davidsmakerworks/fencing-analyzer/FencingAnalyzer.X/configbits.c

/*
 * Fencing Action Analyzer
 * Copyright (c) 2020 David Rice
 * 
 * Configuration bit settings
 * 
 * SET/CLR/INV registers are used when appropriate to avoid
 * R-M-W hazards on MIPS architecture, but "bits" structures
 * are used for readability when no R-M-W hazard exists.
 *
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
 * THE SOFTWARE IS PROVIDED "AS IS", WITHOUT WARRANTY OF ANY KIND, EXPRESS OR
 * IMPLIED, INCLUDING BUT NOT LIMITED TO THE WARRANTIES OF MERCHANTABILITY,
 * FITNESS FOR A PARTICULAR PURPOSE AND NONINFRINGEMENT. IN NO EVENT SHALL THE
 * AUTHORS OR COPYRIGHT HOLDERS BE LIABLE FOR ANY CLAIM, DAMAGES OR OTHER
 * LIABILITY, WHETHER IN AN ACTION OF CONTRACT, TORT OR OTHERWISE, ARISING FROM,
 * OUT OF OR IN CONNECTION WITH THE SOFTWARE OR THE USE OR OTHER DEALINGS IN THE
 * SOFTWARE.
 */

// PIC32MM0064GPL028 Configuration Bit Settings

// 'C' source line config statements

// FDEVOPT
#pragma config SOSCHP = OFF             // Secondary Oscillator High Power Enable bit (SOSC oprerates in normal power mode.)
#pragma config USERID = 0xFFFF          // User ID bits (User ID bits)

// FICD
#pragma config JTAGEN = OFF             // JTAG Enable bit (JTAG is disabled)
#pragma config ICS = PGx1               // ICE/ICD Communication Channel Selection bits (Communicate on PGEC1/PGED1)

// FPOR
#pragma config BOREN = BOR3             // Brown-out Reset Enable bits (Brown-out Reset enabled in hardware; SBOREN bit disabled)
#pragma config RETVR = OFF              // Retention Voltage Regulator Enable bit (Retention regulator is disabled)
#pragma config LPBOREN = ON             // Low Power Brown-out Enable bit (Low power BOR is enabled, when main BOR is disabled)

// FWDT
#pragma config SWDTPS = PS1048576       // Sleep Mode Watchdog Timer Postscale Selection bits (1:1048576)
#pragma config FWDTWINSZ = PS25_0       // Watchdog Timer Window Size bits (Watchdog timer window size is 25%)
#pragma config WINDIS = OFF             // Windowed Watchdog Timer Disable bit (Watchdog timer is in non-window mode)
#pragma config RWDTPS = PS1048576       // Run Mode Watchdog Timer Postscale Selection bits (1:1048576)
#pragma config RCLKSEL = LPRC           // Run Mode Watchdog Timer Clock Source Selection bits (Clock source is LPRC (same as for sleep mode))
#pragma config FWDTEN = OFF             // Watchdog Timer Enable bit (WDT is disabled)

// FOSCSEL
#pragma config FNOSC = FRCDIV           // Oscillator Selection bits (Fast RC oscillator (FRC) with divide-by-N)
#pragma config PLLSRC = FRC             // System PLL Input Clock Selection bit (FRC oscillator is selected as PLL reference input on device reset)
#pragma config SOSCEN = OFF             // Secondary Oscillator Enable bit (Secondary oscillator (SOSC) is disabled)
#pragma config IESO = ON                // Two Speed Startup Enable bit (Two speed startup is enabled)
#pragma config POSCMOD = OFF            // Primary Oscillator Selection bit (Primary oscillator is disabled)
#pragma config OSCIOFNC = OFF           // System Clock on CLKO Pin Enable bit (OSCO pin operates as a normal I/O)
#pragma config SOSCSEL = OFF            // Secondary Oscillator External Clock Enable bit (Crystal is used (RA4 and RB4 are controlled by SOSC))
#pragma config FCKSM = CSECME           // Clock Switching and Fail-Safe Clock Monitor Enable bits (Clock switching is enabled; Fail-safe clock monitor is enabled)

// FSEC
#pragma config CP = OFF                 // Code Protection Enable bit (Code protection is disabled)

// #pragma config statements should precede project file includes.
// Use project enums instead of #define for ON and OFF.
